Alternating/8board-esp32-ledproject/pics/PXL_20251126_200651900.jpg

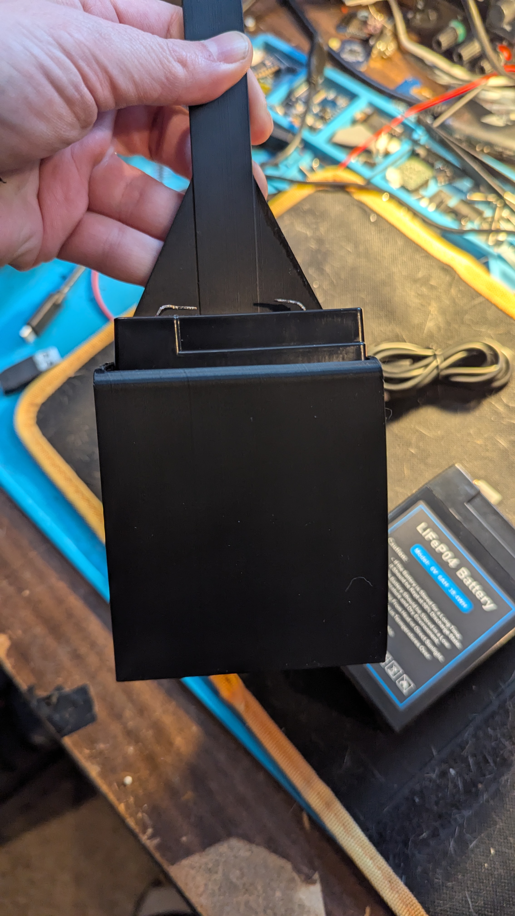
pics/PXL_20251126_200651900.jpg
