Alternating/8board-esp32-ledproject/pics/PXL_20251126_200658001.jpg

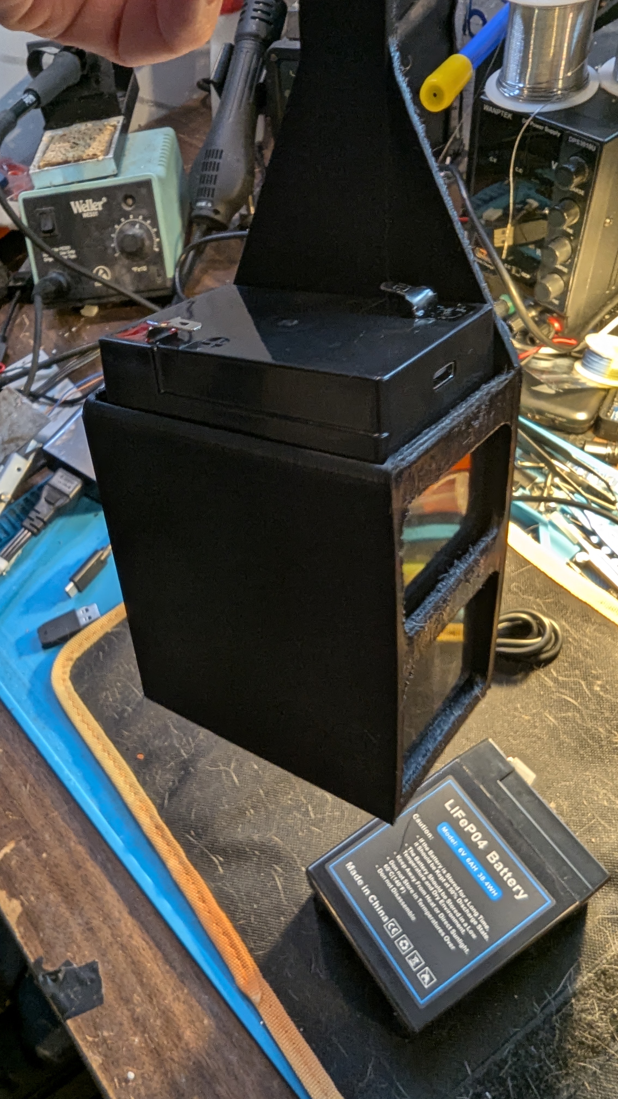
pics/PXL_20251126_200658001.jpg
