Alternating/8board-esp32-ledproject/pics/PXL_20251129_204539264.jpg

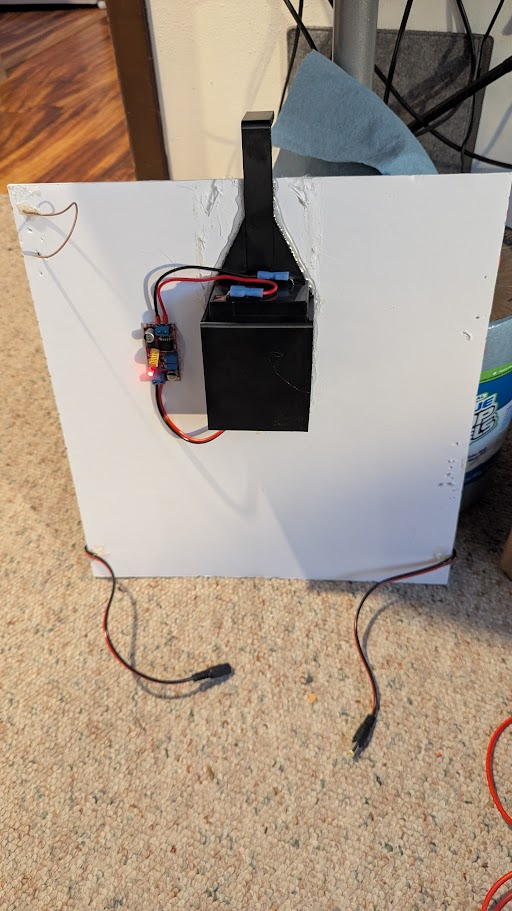
pics/PXL_20251129_204539264.jpg
