Alternating/8board-esp32-ledproject/pics/PXL_20251129_204616917.jpg

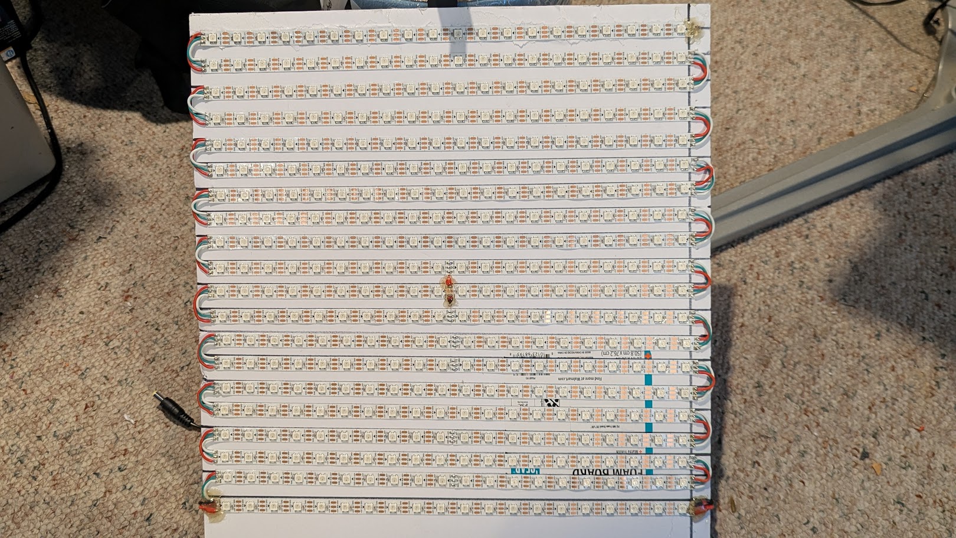
pics/PXL_20251129_204616917.jpg
